SlavaZhuck/NixieClock_KiCad/KiCad_project/KiCad_libs/3d_models/ds3231-real-time-clock-module-1/DS3231 Module.png

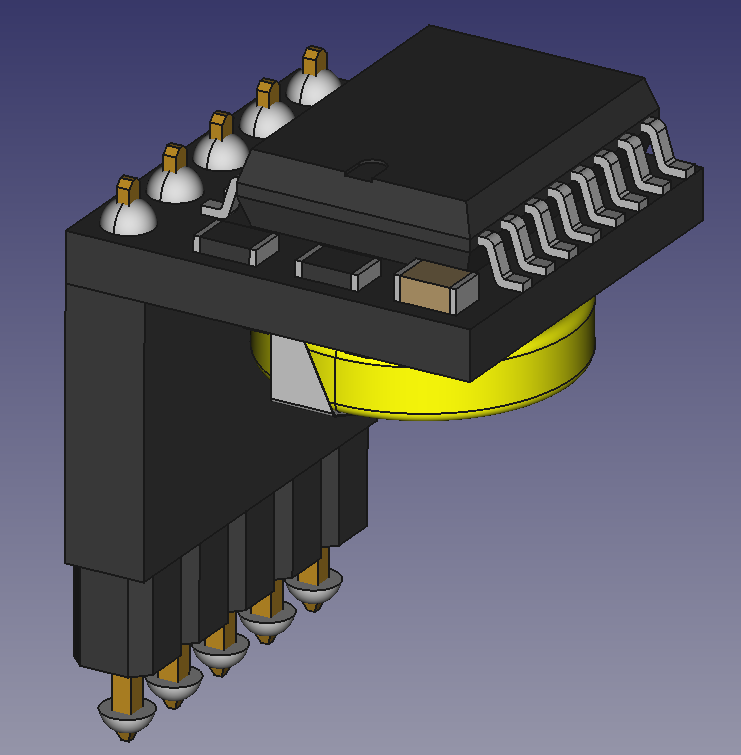
KiCad_project/KiCad_libs/3d_models/ds3231-real-time-clock-module-1/DS3231 Module.png
